ArthurPoncin/sentinel-x/docs/DIGITAL-TWIN.md

# The Digital Twin — our "wow"

A **live 3D replica** of the Sentinel-X outpost rendered in the dashboard (Three.js / react-three-fiber). Real data from every pillar drives the scene in real time. This is what makes the embedded intelligence *visible* to the jury.

## What maps to what

| Real signal (Alert `kind` / telemetry) | Source node | Twin reaction |
|---|---|---|
| Temperature (DHT) | Sentinel | The generator hall's roof glows red as `temp` rises; the air above it ripples while a `thermal` Alert is active |
| Gas (`air`) | Sentinel | Box glows red, a haze around the gas pipe thickens with the reading |
| Presence (`pir`) | Sentinel | The Enclosure's PIR dome blinks, an amber sweep goes round the fence, over its posts and rails |
| Presence or intrusion | Sentinel / Command Post (`vision`) | The **floodlights** on the perimeter come on in white, each lighting a pool on the ground at its foot, and go out when the last of those Alerts is cleared |
| Noise (`noise`) | Sentinel | A wave of light leaves the box and spreads over the socle on each clap, scaled to the Alert's `value` (share of the cycle that was loud) |
| Telemetry frame received | Sentinel → Command Post | An **impulse of white light** leaves the tip of the Enclosure's antenna, rises and fades out: the link is seen to beat, a snapshot a second. None on an Alert, none for the frames already there as the Twin opens, none while the signal is lost. In REPLAY the impulses follow the replayed frames |
| Live feed encrypted (page served over HTTPS, so `wss://`) | Command Post (reverse proxy) | A **padlock and « WSS »** show by the antenna. Read from the page, never claimed: nothing on a plain `ws://` feed, nothing in REPLAY, nothing while the feed is not open |
| Intrusion (vision) | Command Post (`vision`) | The camera's field, a translucent volume from the lens on the Enclosure's roof down to its sector on the ground, lights up and **turns with the real camera** as its servo follows someone (`pan`). The **intruder**, a human figurine in hologram, stands **inside the fence**, on the camera's sight line where `x_norm` places it and as far along it as it is short in the image (`h_norm`): it faces the Enclosure, and walks in toward it as the real person comes nearer the camera, arms and legs in opposition, turned the way it goes. **Each other person** the camera sees (`others`, up to 5 figurines in all) has a figurine too, with a ring at its feet and its four detection brackets; the one the camera follows is told from them by a pin of light, a line to the lens and a label that reads what the model sees and its `confidence`: « PERSONNE · 88 % ». Once the Alert is cleared they all go out, and the one the camera followed leaves its hollow outline where it last stood, still, for about 5 s: the **last known position**; the camera's field goes back to where it rests |
| Predictive drift | Command Post (`predictive`) | The drifting **component pulses orange** *before* the critical threshold |
| `Status` (nominal/elevated/critical) | Command Post | When it rises, the whole scene is flooded in its color for 2 s, then the light goes back to neutral so the signals stand out. The rim light, the ring around the socle, the box's LCD and LED ring stay in its color |
| Live feed lost | Command Post | The whole frame fades to grey and **the picture drops out** like a screen's: snow, strips torn sideways, a bar rolling down the frame, under the notice « Signal lost ». What is shown is no longer live. It clears, in a fade, as soon as the feed is back; nothing before the first connection |
| Alarm (buzzer) | Sentinel | LED ring blinks and buzzer sounds while a `gas` or `thermal` Alert is active. The contract does not carry the Alarm's own state: the Twin does not show it silenced by the Operator |

## What the site says of itself

Not everything on the maquette is driven by the feed. The site carries the signage of a sensitive place, drawn in code like the Enclosure's engraving, in the maquette's neutral tones: color is kept for the `Status` and the signals.

- **Keep out** — a sign « ACCÈS INTERDIT », in AetherCorp's name, on the fence on each side of the gate.
- **Where the risk is** — a hatched danger zone on the ground around the gas tank, and a gas pictogram on the tank. The haze of a leak lies over the marking.
- **Whose site it is** — « AetherCorp » and « OUTPOST 01 » on the generator hall.

Built in #99: see [`../dashboard/README.md`](../dashboard/README.md#digital-twin--featurestwin).

## Where the site stands

The brief places the micro power plants in « zones géographiques isolées et particulièrement hostiles », where staff cannot be kept on site. The maquette says so without a word, and without a signal: none of this reacts to the feed either.

- **Rocks** — faceted rocks lie between the fence and the socle's rim, all round the site but in front of the gate. Nobody clears them.
- **A track that leads nowhere** — it comes in through the gate and goes to the generator hall's door, round the gas tank and the pipe. Outside the gate it stops dead at the socle's rim. It is drawn in the ground, flat: the contour lines run on across it and the camera's sector reads over it.
- **Dust** — a few motes drift slowly over the site, all the one way. They are lit, never glow, and are a few pixels wide: no signal is hidden or imitated.
- **No one** — no vehicle, no figure. The only human the Twin shows is the intruder.

Built in #101: see [`../dashboard/README.md`](../dashboard/README.md#digital-twin--featurestwin).

## What makes the plant eco-responsible

The brief speaks of « micro-centrales énergétiques éco-responsables » and does not name the energy: this is our reading of it. The maquette showed a hall, two chimneys and a gas tank; it now also shows where clean power comes from. None of it reacts to the feed, and its materials are the maquette's neutral ones.

- **A solar field** — fifteen panels in three rows between the Enclosure and the transformer station, leaned toward the entrance.
- **A wind turbine** — a small one beside the generator hall, turned into the wind that carries the dust. Its blades turn slowly, a turn every 6 s, whatever the `Status`.
- **Batteries** — a container alongside the transformer station.
- **The gas stays** — the hall, the tank and the pipe are still there: gas and overheating are the threats the brief names, and what the Twin's reactions are anchored on.

Built in #102: see [`../dashboard/README.md`](../dashboard/README.md#digital-twin--featurestwin).

## Signature features

- **Time-scrubber** — replay a past Incident second-by-second, labelled REPLAY. Lets us script the live demo precisely and re-run it if the network hiccups. Built in #15: see [`../dashboard/README.md`](../dashboard/README.md#time-scrubber--featuresreplay).
- **Director's camera** — the Twin's camera orbits the site, and turns by itself to where an Alert happens the moment it is raised: the intruder on an intrusion, the gas pipe on a gas Alert, the generator hall on a thermal one, the gate on a presence, the box on a predictive drift. It gets there in 2 s by the shortest way round, stays about 6 s, then orbits again; a clap moves nothing. The Operator's hand always wins, and the camera does the same in a replay, in scenario mode and in capture mode. Built in #97: see [`../dashboard/README.md`](../dashboard/README.md#digital-twin--featurestwin).
- **Threat overview** — a single glanceable state fusing cyber + physical + environmental, shown on the twin (not three disconnected widgets).
- **Scenario mode** — a scripted "attack sequence" for the 3-minute live demo and the 60s green-screen teaser. The dashboard plays the reference scenario (gas leak + two PIR detections) on demand, without the network (#15).

## Why it scores

- **Axis 1 (Live demo & integration):** the twin reacting live *is* the proof of end-to-end integration.
- **Axis 3 (Marketing / teaser):** animated 3D over green-screen = strong visual impact in the "Sentinel Drop".
- **Axis 2 (Tech & innovation):** a digital twin fed by encrypted real telemetry reads as genuinely advanced.

## Build notes

- Keep the 3D scene decoupled from data: a small state store (sensor/event feed via WebSocket) → scene subscribes and reacts. Mock the feed so the twin can be built before hardware is ready.
- Low-poly stylized box model (exportable from the Fusion360 CAD used for the physical box) keeps it performant and on-brand.
- Everything reacts to the **same event stream** the real box emits — no fake data path in the final demo.
- The brief asks for a link « sans fil et ultra-sécurisée »: the Enclosure carries an antenna on its side, which beats with the telemetry and says, truthfully, whether the feed the Twin shows is encrypted. The antenna stands still, so its shadow is drawn once with the others; its impulses are light added over the frame and cast none. Built in #103: see [`../dashboard/README.md`](../dashboard/README.md#digital-twin--featurestwin).
- A feed that is lost must not pass for a calm site: besides turning grey, the image drops out (snow, tears, a rolling bar). It is done in the pass that already ends each frame, so the scene is not drawn once more. Built in #104: see [`../dashboard/README.md`](../dashboard/README.md#digital-twin--featurestwin).
- The brief's illustration shows the box on a lattice pylon: the Enclosure stands on a lattice mast, uprights and cross braces on its foot, in neutral steel. It is one shape that stands still, so its shadow is drawn once with the others, and the lens is where it was. Built in #105: see [`../dashboard/README.md`](../dashboard/README.md#digital-twin--featurestwin).
- The floodlights are masts just inside the fence, dark while all is calm. Their light is simulated, a lamp that emits and a pool added over the ground: no light is added to the scene and no shadow is cast, so they cost the frame rate nothing. Built in #100: see [`../dashboard/README.md`](../dashboard/README.md#digital-twin--featurestwin).
- The site reads as the critical infrastructure the brief describes: a chain-link fence under a strand of barbed wire, its gate closed between two pillars. All of it is openwork, so the camera's field, the intruder and the presence's sweep read through it, and its materials stay neutral: color is kept for the `Status` and the signals. Built in #98: see [`../dashboard/README.md`](../dashboard/README.md#digital-twin--featurestwin).
