ArthurPoncin/sentinel-x/docs/dashboard/login-denied.png

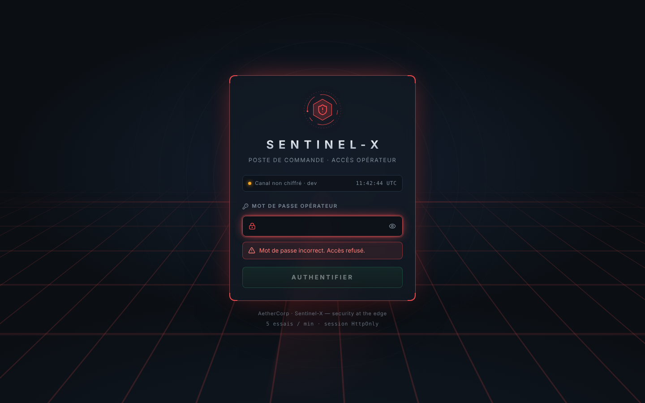
docs/dashboard/login-denied.png
