ArthurPoncin/sentinel-x/docs/dashboard/login-granted.png

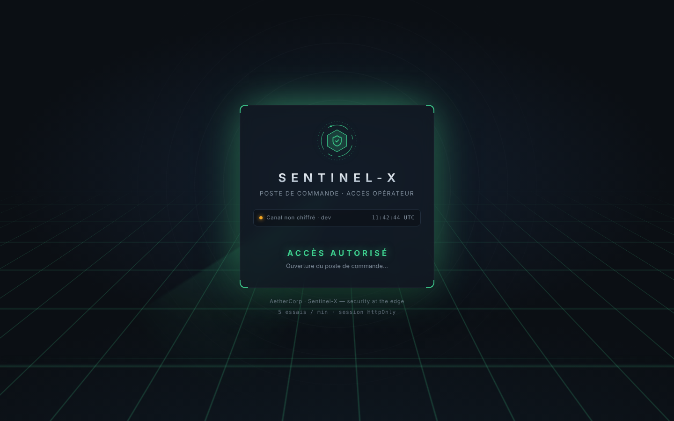
docs/dashboard/login-granted.png
