ArthurPoncin/sentinel-x/docs/dashboard/login.png

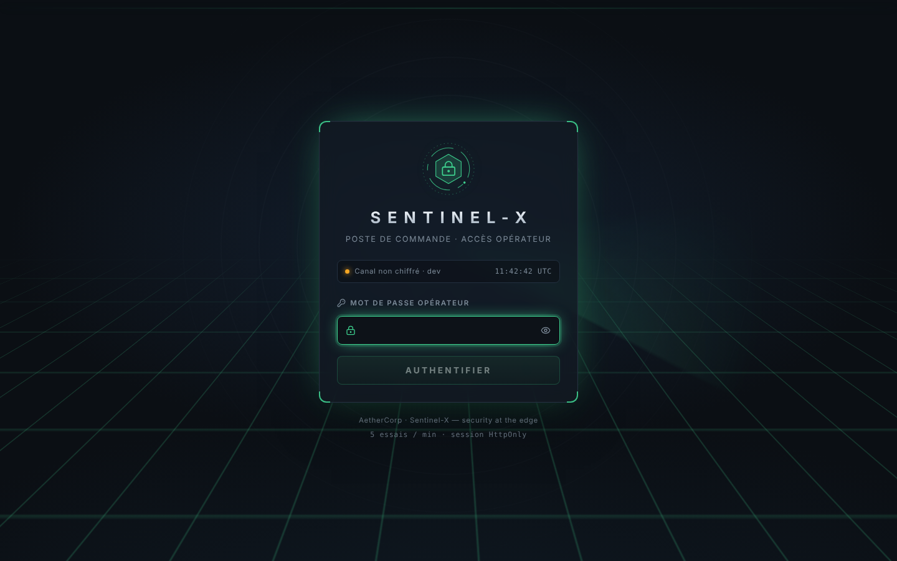
docs/dashboard/login.png
