ArthurPoncin/sentinel-x/docs/twin/enclosure-critical.png

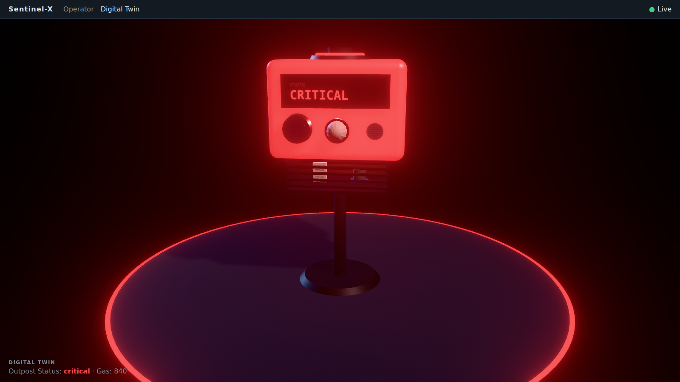
docs/twin/enclosure-critical.png
