ArthurPoncin/sentinel-x/docs/twin/outpost-alone.png

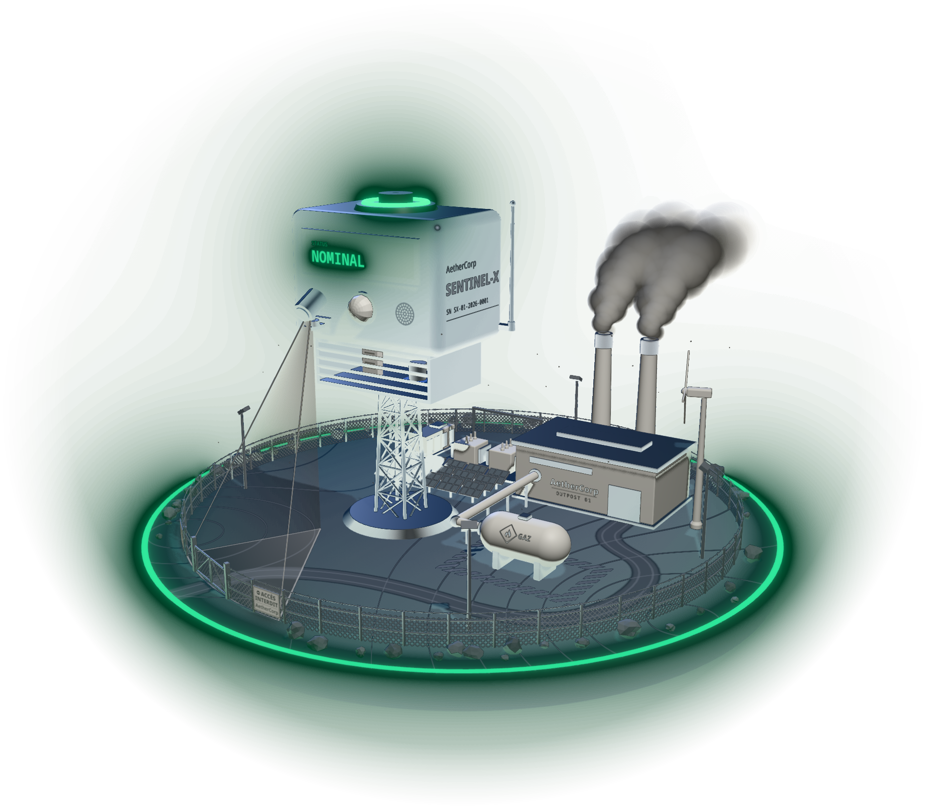
docs/twin/outpost-alone.png
