ArthurPoncin/sentinel-x/ai/vision/tests/test_pan.py

import logging
import sys

import pytest

from sentinel_common.config import ConfigError
from vision import pan
from vision.pan import HALF_STEPS, GpioStepper, PanFollower, SysfsPwmServo, make_pan


def follow(follower: PanFollower, bearing: float | None, start: float, seconds: float, every: float = 0.1) -> list[float]:
    """An inference every `every` seconds that sees the person at `bearing`: how far the camera is turned
    at each."""
    return [follower.aim(bearing, start + i * every) for i in range(1, round(seconds / every) + 1)]


# --- the follower -------------------------------------------------------------------------------------


def test_rests_at_zero_until_there_is_someone_to_turn_to():
    follower = PanFollower()
    assert follower.angle == 0
    assert follower.step(0.0) == 0
    assert follower.rest(1.0) == 0
    assert follower.step(5.0) == 0


def test_turns_to_the_person_followed_and_stops_once_they_are_near_the_middle_of_its_image():
    follower = PanFollower(speed=60, deadband=4)
    angles = follow(follower, 30.0, start=0.0, seconds=2.0)
    assert angles == sorted(angles)
    assert 26 <= angles[-1] <= 30
    # There for good: it does not hunt.
    assert follow(follower, 30.0, start=2.0, seconds=1.0) == [angles[-1]] * 10


def test_turns_the_other_way_just_as_well():
    right, left = PanFollower(), PanFollower()
    assert follow(left, -30.0, 0.0, 2.0) == [-angle for angle in follow(right, 30.0, 0.0, 2.0)]


def test_never_turns_faster_than_its_speed():
    follower = PanFollower(speed=60)
    follower.step(0.0)
    angles = [0.0, *follow(follower, 80.0, start=0.0, seconds=1.0, every=0.05)]
    assert all(later - earlier <= 60 * 0.05 + 1e-9 for earlier, later in zip(angles, angles[1:]))
    assert angles[-1] > 40


def test_leaves_someone_within_the_deadband_where_they_are():
    follower = PanFollower(deadband=4)
    assert follow(follower, 3.9, 0.0, 1.0) == [0.0] * 10
    assert follow(follower, -3.9, 1.0, 1.0) == [0.0] * 10


def test_never_turns_past_its_travel():
    follower = PanFollower(low=-45, high=60)
    assert follow(follower, 170.0, 0.0, 5.0)[-1] == 60
    assert follow(follower, -170.0, 5.0, 5.0)[-1] == -45


def test_stays_where_it_is_when_the_person_followed_is_not_seen():
    follower = PanFollower()
    reached = follow(follower, 40.0, 0.0, 0.5)[-1]
    assert 0 < reached < 40
    # It stops where the inference that misses them finds it.
    held = follow(follower, None, 0.5, 2.0)
    assert held == [held[0]] * 20
    assert 0 <= held[0] - reached <= 60 * 0.1 + 1e-9


def test_goes_back_to_where_it_rests_once_the_intrusion_is_over_slowly():
    follower = PanFollower(speed=60, home_speed=30)
    follow(follower, 45.0, 0.0, 3.0)
    turned = follower.angle
    assert turned > 40
    follower.rest(3.0)
    assert follower.step(4.0) == pytest.approx(turned - 30)
    assert follower.step(10.0) == 0
    assert follower.step(11.0) == 0


def test_is_the_same_whatever_the_rate_it_is_stepped_at():
    coarse, fine = PanFollower(), PanFollower()
    for follower in (coarse, fine):
        follower.aim(50.0, 0.0)
    coarse.step(0.5)
    for i in range(1, 51):
        fine.step(i * 0.01)
    assert fine.angle == pytest.approx(coarse.angle)


def test_a_clock_that_goes_back_turns_nothing():
    follower = PanFollower()
    follower.aim(50.0, 10.0)
    assert follower.step(9.0) == 0
    assert follower.step(10.5) == pytest.approx(30)


def test_remembers_how_far_it_was_turned_when_an_image_was_taken():
    follower = PanFollower(speed=60, gain=1)
    follower.aim(60.0, 0.0)
    for i in range(1, 11):
        follower.step(i * 0.1)
    assert follower.angle == pytest.approx(60)
    assert follower.angle_at(0.0) == 0
    assert follower.angle_at(0.5) == pytest.approx(30)
    assert follower.angle_at(0.25) == pytest.approx(15)
    # Later than now: where it is. Further back than it remembers: the oldest it does.
    assert follower.angle_at(5.0) == pytest.approx(60)
    assert follower.angle_at(-1.0) == 0
    follower.step(10.0)
    assert follower.angle_at(0.5) == pytest.approx(60)


def test_the_way_home_is_taken_at_its_speed_and_ends_where_it_rests():
    follower = PanFollower(speed=60, gain=1)
    assert follower.way_home(0.05) == []
    follower.aim(45.0, 0.0)
    follower.step(2.0)
    way = follower.way_home(0.05)
    assert way[-1] == 0
    assert len(way) == 15
    assert all(abs(later - earlier) <= 3 + 1e-9 for earlier, later in zip([45.0, *way], way))


def idle(follower: PanFollower, start: float, seconds: float, every: float = 0.1) -> list[float]:
    """An inference every `every` seconds with no intrusion: how far the camera is turned at each."""
    return [follower.rest(start + i * every) for i in range(1, round(seconds / every) + 1)]


def test_waits_where_it_lost_them_for_a_while_before_going_back_to_where_it_rests():
    follower = PanFollower(speed=60, home_speed=30, home_after=2)
    follow(follower, 45.0, 0.0, 3.0)
    turned = follower.angle
    # 2 s where it is: they may come back into its image.
    follower.rest(3.0)
    assert [follower.step(3.0 + i * 0.1) for i in range(1, 21)] == [turned] * 20
    assert follower.step(6.0) == pytest.approx(turned - 30)
    assert follower.step(10.0) == 0


def test_once_back_where_it_rests_it_patrols_slowly_from_one_side_to_the_other():
    follower = PanFollower(patrol=30, patrol_speed=10)
    follower.rest(0.0)
    angles = idle(follower, 0.0, 15.0)
    # Right first, 30 degrees in 3 s, then all the way left in 6 s, then right again.
    assert angles[29] == pytest.approx(30)
    assert angles[89] == pytest.approx(-30)
    assert angles[-1] == pytest.approx(30)
    assert min(angles) == pytest.approx(-30) and max(angles) == pytest.approx(30)
    assert all(abs(later - earlier) <= 1 + 1e-9 for earlier, later in zip(angles, angles[1:]))


def test_patrols_between_inferences_too():
    follower = PanFollower(patrol=30, patrol_speed=10)
    follower.rest(0.0)
    angles = [follower.step(i * 0.5) for i in range(1, 25)]
    assert angles[5] == pytest.approx(30) and angles[17] == pytest.approx(-30)


def test_goes_back_to_where_it_rests_before_it_patrols():
    follower = PanFollower(home_speed=30, patrol=30, patrol_speed=10)
    follow(follower, -60.0, 0.0, 3.0)
    assert follower.angle < -50
    angles = idle(follower, 3.0, 5.0)
    back = next(i for i, angle in enumerate(angles) if angle == 0)
    assert angles[:back] == sorted(angles[:back])
    # From there, slowly to the right.
    assert 0 < angles[back + 10] <= 10 + 1e-9


def test_its_patrol_keeps_to_its_travel():
    follower = PanFollower(low=-10, high=90, patrol=30, patrol_speed=10)
    follower.rest(0.0)
    angles = idle(follower, 0.0, 10.0)
    assert min(angles) == pytest.approx(-10) and max(angles) == pytest.approx(30)


@pytest.mark.parametrize("low, high, ends", [(0, 90, (0, 30)), (-90, 0, (-30, 0))])
def test_patrols_on_one_side_when_it_rests_at_an_end_of_its_travel(low, high, ends):
    follower = PanFollower(low=low, high=high, patrol=30, patrol_speed=10)
    follower.rest(0.0)
    angles = idle(follower, 0.0, 10.0)
    assert (min(angles), max(angles)) == pytest.approx(ends)


def test_turns_to_an_intruder_seen_on_patrol_and_patrols_afresh_after():
    follower = PanFollower(patrol=30, patrol_speed=10, home_after=1)
    idle(follower, 0.0, 2.0)
    assert 0 < follower.angle < 30
    assert 46 <= follow(follower, 50.0, 2.0, 2.0)[-1] <= 50
    # Waits, goes back, then patrols again from where it rests: to the right first.
    angles = idle(follower, 4.0, 5.0)
    assert angles[:10] == [angles[0]] * 10
    back = angles.index(0)
    assert angles[:back] == sorted(angles[:back], reverse=True)
    assert 0 < angles[-1] <= 30 and angles[back:] == sorted(angles[back:])


@pytest.mark.parametrize(
    "settings",
    [
        {"home_after": -1},
        {"patrol": -5},
        {"patrol_speed": 0},
        {"low": 10, "high": 90},
        {"low": -90, "high": -10},
        {"low": 0, "high": 0},
        {"speed": 0},
        {"home_speed": -1},
        {"deadband": -1},
        {"gain": 0},
        {"gain": 1.5},
        {"memory": 0},
        {"speed": float("nan")},
    ],
)
def test_the_follower_refuses_invalid_settings(settings):
    with pytest.raises(ValueError):
        PanFollower(**settings)


# --- the servo ----------------------------------------------------------------------------------------


@pytest.fixture
def channel(tmp_path):
    """A PWM channel's directory, as the kernel shows one that was just exported."""
    for name in ("period", "duty_cycle", "enable"):
        (tmp_path / name).write_text("0")
    return tmp_path


def state(channel) -> dict[str, int]:
    return {name: int((channel / name).read_text()) for name in ("period", "duty_cycle", "enable")}


def test_opens_at_rest_with_a_pulse_every_20_ms(channel):
    servo = SysfsPwmServo(str(channel))
    servo.open()
    assert state(channel) == {"period": 20_000_000, "duty_cycle": 1_500_000, "enable": 1}


def test_the_pulse_says_the_angle_from_one_end_of_its_travel_to_the_other(channel):
    servo = SysfsPwmServo(str(channel), low=-90, high=90, min_us=500, max_us=2500)
    assert [servo.pulse_us(angle) for angle in (-90, -45, 0, 45, 90)] == [500, 1000, 1500, 2000, 2500]
    servo.open()
    servo.turn(45.0)
    assert state(channel)["duty_cycle"] == 2_000_000
    # Past its travel is the end of it.
    servo.turn(400.0)
    assert state(channel)["duty_cycle"] == 2_500_000
    servo.turn(-400.0)
    assert state(channel)["duty_cycle"] == 500_000


def test_a_servo_mounted_the_other_way_up_turns_the_other_way_for_the_same_angle(channel):
    servo = SysfsPwmServo(str(channel), invert=True)
    assert [servo.pulse_us(angle) for angle in (-90, 0, 90)] == [2500, 1500, 500]


def test_a_travel_that_is_not_half_a_turn_and_pulses_that_are_not_the_usual(channel):
    servo = SysfsPwmServo(str(channel), low=-60, high=120, min_us=600, max_us=2400)
    assert [servo.pulse_us(angle) for angle in (-60, 30, 120)] == [600, 1500, 2400]


def test_writes_the_pulse_only_when_it_changes(channel):
    servo = SysfsPwmServo(str(channel))
    servo.open()
    servo.turn(10.0)
    (channel / "duty_cycle").write_text("touched")
    servo.turn(10.0)
    assert (channel / "duty_cycle").read_text() == "touched"
    servo.turn(10.5)
    assert int((channel / "duty_cycle").read_text()) == round((1500 + 10.5 * 2000 / 180) * 1000)


def test_lets_the_servo_go_when_closed(channel):
    servo = SysfsPwmServo(str(channel))
    servo.open()
    servo.turn(30.0)
    servo.close()
    assert state(channel)["enable"] == 0
    # Closed twice, or never opened: nothing to do.
    (channel / "enable").write_text("7")
    servo.close()
    assert state(channel)["enable"] == 7


def test_a_channel_that_is_not_there_stops_nothing_and_is_tried_again_later(tmp_path, caplog):
    now = [0.0]
    missing = tmp_path / "pwm0"
    servo = SysfsPwmServo(str(missing), retry=5.0, clock=lambda: now[0])
    with caplog.at_level(logging.WARNING):
        servo.open()
        for _ in range(50):
            now[0] += 0.05
            servo.turn(20.0)
    assert len(caplog.records) == 1 and "unavailable" in caplog.text
    # The channel comes: the next try finds it, and turns to where the camera is told to be.
    missing.mkdir()
    for name in ("period", "duty_cycle", "enable"):
        (missing / name).write_text("0")
    now[0] = 5.5
    servo.turn(20.0)
    assert state(missing) == {"period": 20_000_000, "duty_cycle": round((1500 + 20 * 2000 / 180) * 1000), "enable": 1}


@pytest.mark.parametrize(
    "args, settings",
    [
        (("",), {}),
        (("/pwm",), {"low": 90, "high": -90}),
        (("/pwm",), {"min_us": 2500, "max_us": 500}),
        (("/pwm",), {"min_us": 0}),
        (("/pwm",), {"max_us": 25000}),
    ],
)
def test_the_servo_refuses_invalid_settings(args, settings):
    with pytest.raises(ValueError):
        SysfsPwmServo(*args, **settings)


# --- the stepper --------------------------------------------------------------------------------------


class Board:
    """A ULN2003 board as the stepper sees it: what it set on IN1 to IN4, in order, and whether it was given
    back."""

    def __init__(self) -> None:
        self.written: list[tuple[int, ...]] = []
        self.released = False

    def put(self, values) -> None:
        self.written.append(tuple(values))

    def release(self) -> None:
        self.released = True

    def steps(self) -> list[tuple[int, ...]]:
        """The half-steps it was sent, the coils let go left out."""
        return [values for values in self.written if any(values)]


def stepper(board: Board, **settings) -> GpioStepper:
    settings.setdefault("sleep", lambda seconds: None)
    return GpioStepper((6, 13, 19, 26), open_lines=lambda chip, pins: board, **settings)


def test_a_quarter_turn_is_a_quarter_of_its_half_steps():
    drive = stepper(Board())
    assert [drive.steps_for(angle) for angle in (-90, 0, 45, 90, 360)] == [-1024, 0, 512, 1024, 4096]
    assert [stepper(Board(), invert=True).steps_for(angle) for angle in (-90, 90)] == [1024, -1024]
    assert stepper(Board(), steps_per_turn=2048).steps_for(90) == 512


def test_turns_half_step_by_half_step_then_lets_the_coils_go():
    board = Board()
    drive = stepper(board)
    drive.open()
    drive.turn(90.0)
    drive.close()
    steps = board.steps()
    assert len(steps) == 1024
    assert steps[0] == HALF_STEPS[1] and steps[-1] == HALF_STEPS[1024 % 8]
    # Never a half-step skipped: each is the next one in the cycle.
    assert all(HALF_STEPS.index(after) == (HALF_STEPS.index(before) + 1) % 8 for before, after in zip(steps, steps[1:]))
    # There, the coils go, and closed, the lines too.
    assert board.written[-1] == (0, 0, 0, 0)
    assert board.released


def test_turns_back_the_other_way_to_where_it_was_last_told():
    board = Board()
    drive = stepper(board)
    drive.open()
    drive.turn(10.0)
    drive.turn(-10.0)
    drive.close()
    # However far it went toward 10°, it ends at -10°: the half-step of -114 is the last one.
    assert board.steps()[-1] == HALF_STEPS[drive.steps_for(-10.0) % 8]
    steps = board.steps()
    assert all(abs(HALF_STEPS.index(after) - HALF_STEPS.index(before)) in (1, 7) for before, after in zip(steps, steps[1:]))


def test_never_steps_faster_than_its_pace():
    board, pauses = Board(), []
    drive = stepper(board, step_s=0.003, sleep=pauses.append)
    drive.open()
    drive.turn(45.0)
    drive.close()
    assert pauses == [0.003] * 512


def test_a_chip_that_is_not_there_stops_nothing_and_is_tried_again_later(caplog):
    now, board, missing = [0.0], Board(), [True]

    def open_lines(chip, pins):
        if missing[0]:
            raise FileNotFoundError(2, "No such file or directory", chip)
        return board

    drive = GpioStepper((6, 13, 19, 26), open_lines=open_lines, retry=5.0, clock=lambda: now[0], sleep=lambda seconds: None)
    with caplog.at_level(logging.WARNING):
        drive.open()
        for _ in range(50):
            now[0] += 0.05
            drive.turn(20.0)
    assert len(caplog.records) == 1 and "unavailable" in caplog.text
    assert board.written == []
    # The board comes: the next try finds it, and turns to where the camera is told to be.
    missing[0] = False
    now[0] = 5.5
    drive.turn(20.0)
    drive.close()
    assert len(board.steps()) == drive.steps_for(20.0)


def test_remembers_how_far_it_had_turned_the_camera_when_an_image_was_taken():
    # A clock that only the motor's own pauses move: its half-step k is counted at k times 2 ms.
    now = [0.0]

    def pause(seconds: float) -> None:
        now[0] += seconds

    def turned(**settings) -> GpioStepper:
        now[0] = 0.0
        drive = stepper(Board(), clock=lambda: now[0], sleep=pause, **settings)
        drive.open()
        drive.turn(100 * 360 / 4096)
        drive.close()
        return drive

    drive = turned()
    assert [drive.angle_at(moment) for moment in (0.0, 0.001)] == [0, 0]
    assert drive.angle_at(0.101) == pytest.approx(50 * 360 / 4096)
    assert drive.angle_at(0.151) == pytest.approx(75 * 360 / 4096)
    assert drive.angle_at(60.0) == pytest.approx(100 * 360 / 4096)
    # The angle it was told, whichever way it is mounted.
    assert turned(invert=True).angle_at(0.101) == pytest.approx(50 * 360 / 4096)
    # Further back than its memory, 25 of these half-steps: where the oldest it remembers started from.
    assert 70 <= turned(memory=0.05).angle_at(0.0) / (360 / 4096) <= 80
    # And one that never turned was where it rests.
    assert stepper(Board()).angle_at(5.0) == 0


def test_closed_twice_or_never_opened_does_nothing():
    board = Board()
    drive = stepper(board)
    drive.close()
    assert board.written == [] and not board.released
    drive.open()
    drive.close()
    drive.close()
    assert board.released


@pytest.mark.parametrize(
    "pins, settings",
    [
        ((6, 13, 19), {}),
        ((6, 13, 19, 19), {}),
        ((6, 13, 19, -1), {}),
        ((6, 13, 19, 26), {"chip": ""}),
        ((6, 13, 19, 26), {"steps_per_turn": 0}),
        ((6, 13, 19, 26), {"step_s": 0}),
        ((6, 13, 19, 26), {"memory": 0}),
    ],
)
def test_the_stepper_refuses_invalid_settings(pins, settings):
    with pytest.raises(ValueError):
        GpioStepper(pins, **settings)


# --- PAN_DRIVE ----------------------------------------------------------------------------------------


@pytest.fixture(autouse=True)
def no_pan_settings(monkeypatch):
    for name in (
        "PAN_PWM_DIR", "PAN_MIN_DEG", "PAN_MAX_DEG", "PAN_MIN_US", "PAN_MAX_US", "PAN_INVERT", "PAN_SPEED_DEG_S", "PAN_DEADBAND_DEG",
        "PAN_STEPPER_PINS", "PAN_GPIO_CHIP", "PAN_STEPS_PER_TURN", "PAN_STEP_MS",
        "PAN_HOME_AFTER_S", "PAN_PATROL_DEG", "PAN_PATROL_SPEED_DEG_S",
    ):
        monkeypatch.delenv(name, raising=False)


def test_a_fixed_camera_has_no_pan():
    assert make_pan("none") is None


def test_the_pwm_drive_takes_its_channel_its_travel_and_its_pulses_from_the_environment(channel, monkeypatch):
    monkeypatch.setenv("PAN_PWM_DIR", str(channel))
    monkeypatch.setenv("PAN_MIN_DEG", "-60")
    monkeypatch.setenv("PAN_MAX_DEG", "120")
    monkeypatch.setenv("PAN_MIN_US", "600")
    monkeypatch.setenv("PAN_MAX_US", "2400")
    follower, drive = make_pan("pwm")
    assert drive.name == "pwm"
    assert [drive.pulse_us(angle) for angle in (-60, 30, 120)] == [600, 1500, 2400]
    # The follower keeps to the same travel.
    assert follow(follower, 170.0, 0.0, 5.0)[-1] == 120
    assert follow(follower, -170.0, 5.0, 8.0)[-1] == -60


def test_the_stepper_drive_takes_its_pins_and_its_half_steps_from_the_environment(monkeypatch):
    monkeypatch.setenv("PAN_STEPPER_PINS", "17, 27, 22, 23")
    monkeypatch.setenv("PAN_STEPS_PER_TURN", "2048")
    monkeypatch.setenv("PAN_INVERT", "true")
    follower, drive = make_pan("stepper")
    assert drive.name == "stepper"
    assert drive._pins == (17, 27, 22, 23)
    assert drive.steps_for(90) == -512
    assert follower.angle == 0


def test_waits_2_s_then_patrols_30_degrees_either_way_at_8_a_second_unless_told_otherwise(monkeypatch):
    follower, _ = make_pan("stepper")
    follower.rest(0.0)
    angles = idle(follower, 0.0, 12.0)
    assert set(angles[:20]) == {0.0}
    # Then 30 degrees in 3.75 s, and back.
    assert angles[19 + 37] < 30 and angles[19 + 38] == 30 and angles[-1] < 30
    monkeypatch.setenv("PAN_HOME_AFTER_S", "0")
    monkeypatch.setenv("PAN_PATROL_DEG", "0")
    follower, _ = make_pan("stepper")
    assert set(idle(follower, 0.0, 12.0)) == {0.0}


@pytest.mark.parametrize(
    "name, variables",
    [
        ("dc-motor", {}),
        ("stepper", {"PAN_STEPPER_PINS": "6,13,19"}),
        ("stepper", {"PAN_STEPPER_PINS": "6,13,19,19"}),
        ("stepper", {"PAN_STEPPER_PINS": "six,13,19,26"}),
        ("stepper", {"PAN_STEP_MS": "0"}),
        ("pwm", {"PAN_MIN_DEG": "10"}),
        ("pwm", {"PAN_MAX_DEG": "-10"}),
        ("pwm", {"PAN_MIN_DEG": "0", "PAN_MAX_DEG": "0"}),
        ("pwm", {"PAN_MIN_US": "2500", "PAN_MAX_US": "500"}),
        ("pwm", {"PAN_SPEED_DEG_S": "0"}),
        ("pwm", {"PAN_HOME_AFTER_S": "-1"}),
        ("pwm", {"PAN_PATROL_DEG": "-30"}),
        ("pwm", {"PAN_PATROL_SPEED_DEG_S": "0"}),
        ("pwm", {"PAN_INVERT": "maybe"}),
    ],
)
def test_refuses_a_drive_or_a_setting_that_is_not_one(name, variables, monkeypatch):
    for variable, value in variables.items():
        monkeypatch.setenv(variable, value)
    with pytest.raises(ConfigError):
        make_pan(name)


# --- python -m vision.pan -----------------------------------------------------------------------------


@pytest.fixture
def wired(monkeypatch):
    """The stack's stepper on a board of the tests, in place of the Pi's GPIO."""
    board = Board()
    monkeypatch.setattr(pan, "_gpiod_lines", lambda chip, pins: board)
    monkeypatch.setenv("PAN_DRIVE", "stepper")
    monkeypatch.setenv("PAN_STEP_MS", "0.5")
    return board


def test_the_command_turns_the_camera_by_as_much_as_asked_and_leaves_it_there(wired, monkeypatch, capsys):
    monkeypatch.setattr(sys, "argv", ["vision.pan", "-10"])
    pan.main()
    steps = wired.steps()
    assert len(steps) == 114 and steps[0] == HALF_STEPS[-1] and wired.written[-1] == (0, 0, 0, 0)
    assert wired.released
    assert "Turned by -10.0 degrees" in capsys.readouterr().out


def test_the_command_turns_the_camera_no_further_than_its_travel(wired, monkeypatch, capsys):
    monkeypatch.setenv("PAN_MAX_DEG", "5")
    monkeypatch.setattr(sys, "argv", ["vision.pan", "400"])
    pan.main()
    assert len(wired.steps()) == 57
    assert "Turned by +5.0 degrees" in capsys.readouterr().out


@pytest.mark.parametrize(
    "arguments, variables, message",
    [
        ([], {}, "Usage"),
        (["left"], {}, "Usage"),
        (["10", "20"], {}, "Usage"),
        (["10"], {"PAN_DRIVE": ""}, "PAN_DRIVE=none"),
        (["10"], {"PAN_STEPPER_PINS": "6,13"}, "PAN_STEPPER_PINS"),
    ],
)
def test_the_command_says_what_it_cannot_do(wired, monkeypatch, arguments, variables, message):
    for variable, value in variables.items():
        monkeypatch.setenv(variable, value)
    monkeypatch.setattr(sys, "argv", ["vision.pan", *arguments])
    with pytest.raises(SystemExit, match=message):
        pan.main()
    assert wired.written == []


def test_the_command_says_so_when_the_motor_is_not_there(monkeypatch):
    def no_chip(chip, pins):
        raise FileNotFoundError(2, "No such file or directory", chip)

    monkeypatch.setattr(pan, "_gpiod_lines", no_chip)
    monkeypatch.setenv("PAN_DRIVE", "stepper")
    monkeypatch.setattr(sys, "argv", ["vision.pan", "10"])
    with pytest.raises(SystemExit, match="did not turn"):
        pan.main()
